wekospace/kiss_8006/python/tests/test_buttons.py

#!/usr/bin/env python3

import sys, os
import time
from RPi import GPIO

sys.path.append(os.path.join(os.path.realpath(os.path.dirname(__file__)), '../'))

from kmm import *

debug=False

irq = 22
fp = Kmm(async=True,debug=debug)

def int_to_chr(i):
    if(i == 0xaa):
        return '0xaa'
    else:
        return chr(i)

def read_inputs(pin):
    if debug: print("IRQ on:" + str(pin))
    fp.request_reception()

def button_received(button):
    print(button)
    fp.set_text(str(button))
    input = GPIO.input(irq)
    if debug: print("input: "+str(input))
    if input != 1: read_inputs(None)

GPIO.setmode(GPIO.BOARD)
GPIO.setup(irq,GPIO.IN)
GPIO.add_event_detect(irq, GPIO.FALLING, callback=read_inputs)

fp.register_input_button_callback(button_received)

fp.set_text('Hit a key')

while(GPIO.input(irq) == 0):
    read_inputs("Zzz")

while True:
    time.sleep(1)
    #print "I'm alive !"
    input = GPIO.input(irq)
    if input != 1: print("Error: IRQ pin value is " + str(GPIO.input(irq)))
