wekospace/kiss_8006/python/tests/test_display.py

#!/usr/bin/env python3

import sys, os
import time
from datetime import datetime

sys.path.append(os.path.join(os.path.realpath(os.path.dirname(__file__)), '../'))

from kmm import *

fp = Kmm(async=True)
fp.clear()

#  _____         _
# |_   _|____  _| |_
#   | |/ _ \ \/ / __|
#   | |  __/>  <| |_
#   |_|\___/_/\_\\__|
#
fp.set_text("Hello")
time.sleep(1)
fp.set_flash_text(10, "Flash")
time.sleep(2)
fp.set_scrolling_text(1, 2, "This text will be displayed twice")
time.sleep(3)
fp.set_text("123456789012")
time.sleep(1)
fp.set_text("@&é\"'(§è!çà)")
time.sleep(1)
fp.set_text("#-^$ù`,;:=_*")
time.sleep(1)
fp.set_text("%£?./+€~|<>ë") # € is replaced
time.sleep(1)
fp.set_text("“‘{¶«¡Çø}—É[")
time.sleep(1)
fp.set_text("å»ÛÁØ]")
time.sleep(1)

#  _   _                           _
# | \ | |_   _ _ __ ___   ___ _ __(_) ___
# |  \| | | | | '_ ` _ \ / _ \ '__| |/ __|
# | |\  | |_| | | | | | |  __/ |  | | (__
# |_| \_|\__,_|_| |_| |_|\___|_|  |_|\___|
#

for i in range(0, 3):
    now = datetime.now()
    fp.set_time(now.strftime("0%H%M%S"))
    time.sleep(1)
fp.set_time(None)
time.sleep(1)

now = datetime.now()
fp.set_track_clock(now.strftime("0%H%M"))
time.sleep(1)
fp.set_track_clock(None)
time.sleep(1)

now = datetime.now()
fp.set_clock(now.strftime("0%H%M"))
time.sleep(1)
fp.set_clock(None)
time.sleep(1)

#  _             _
# | |    ___  __| |
# | |   / _ \/ _` |
# | |__|  __/ (_| |
# |_____\___|\__,_|
#

fp.set_power_led(LedColor.red)
time.sleep(1)
fp.set_power_led(LedColor.green)
time.sleep(1)
fp.set_power_led(LedColor.orange)
time.sleep(1)
fp.set_power_led(LedColor.off)
time.sleep(1)


#'VA' => All, only 'O' works after
#'VO' => Blank, only 'A' works after
#'VP' => Blank, unable to restart
#'CP' => device always reply 0xff after that
#blacklist = [
#    'VA', 'VO', 'VP',
#    'CP',
#]
#
#for i in range(ord('A'), ord('Z')+1):
#    command = 'V' + chr(i) + "123456"
#    if command[0:2] in blacklist:
#        print("blacklisted command: " + chr(i))
#        continue
#    print(command)
#    fp.set_text(command)
#    fp.set_clock('%0*d' % (5, i))
#    fp.set_track_clock('%0*d' % (5, i))
#    time.sleep(1)
#    print("---")
#    print(fp.send_command(command))
#    print(fp.send_raw_data([0xaa] * 20))
#    print("---")
#    time.sleep(3)

del fp
